skysmith/magic-character-box/tests/test_wifi.py

from __future__ import annotations

import json
import subprocess
import unittest

from magic_box.wifi import WifiController


class WifiControllerTests(unittest.TestCase):
    def test_status_uses_privileged_helper_when_available(self) -> None:
        runner = _FakeRunner(
            {
                ("/usr/local/bin/magic-character-box-wifi-control", "radio-status"): subprocess.CompletedProcess(
                    [], 0, "enabled\n", ""
                ),
                ("/usr/local/bin/magic-character-box-wifi-control", "device-status"): subprocess.CompletedProcess(
                    [], 0, "wlan0:wifi:connected:Mini Cottage\n", ""
                ),
            }
        )
        controller = WifiController(
            nmcli=None,
            helper="/usr/local/bin/magic-character-box-wifi-control",
            sudo="",
            runner=runner,
        )

        status = controller.status()

        self.assertTrue(status.available)
        self.assertTrue(status.connected)
        self.assertEqual(status.ssid, "Mini Cottage")
        self.assertEqual(
            runner.commands,
            [
                ("/usr/local/bin/magic-character-box-wifi-control", "radio-status"),
                ("/usr/local/bin/magic-character-box-wifi-control", "device-status"),
            ],
        )

    def test_connect_uses_helper_without_leaking_password_in_result(self) -> None:
        runner = _FakeRunner(
            {
                ("/usr/local/bin/magic-character-box-wifi-control", "connect-stdin"): subprocess.CompletedProcess(
                    [], 0, "connected\n", ""
                ),
                ("/usr/local/bin/magic-character-box-wifi-control", "radio-status"): subprocess.CompletedProcess(
                    [], 0, "enabled\n", ""
                ),
                ("/usr/local/bin/magic-character-box-wifi-control", "device-status"): subprocess.CompletedProcess(
                    [], 0, "wlan0:wifi:connected:Mini Cottage\n", ""
                ),
            }
        )
        controller = WifiController(
            nmcli=None,
            helper="/usr/local/bin/magic-character-box-wifi-control",
            sudo="",
            runner=runner,
        )

        result = controller.connect("Mini Cottage", "private pass")

        self.assertTrue(result.ok)
        self.assertEqual(result.message, "Connected to Mini Cottage.")
        self.assertNotIn("private pass", result.to_dict()["message"])
        self.assertEqual(
            runner.commands[0],
            ("/usr/local/bin/magic-character-box-wifi-control", "connect-stdin"),
        )
        self.assertNotIn("private pass", " ".join(runner.commands[0]))
        self.assertEqual(
            json.loads(runner.inputs[0] or ""),
            {"ssid": "Mini Cottage", "password": "private pass"},
        )

    def test_connect_recovers_from_r24_helper_missing_json_import(self) -> None:
        runner = _FakeRunner(
            {
                ("/usr/local/bin/magic-character-box-wifi-control", "connect-stdin"): subprocess.CompletedProcess(
                    [], 1, "", "NameError: name 'json' is not defined\n"
                ),
                ("/usr/bin/nmcli", "--ask", "device", "wifi", "connect", "Mini Cottage"):
                    subprocess.CompletedProcess([], 0, "connected\n", ""),
                ("/usr/local/bin/magic-character-box-wifi-control", "radio-status"): subprocess.CompletedProcess(
                    [], 0, "enabled\n", ""
                ),
                ("/usr/local/bin/magic-character-box-wifi-control", "device-status"): subprocess.CompletedProcess(
                    [], 0, "wlan0:wifi:connected:Mini Cottage\n", ""
                ),
            }
        )
        controller = WifiController(
            nmcli="/usr/bin/nmcli",
            helper="/usr/local/bin/magic-character-box-wifi-control",
            sudo="",
            runner=runner,
        )

        result = controller.connect("Mini Cottage", "private pass")

        self.assertTrue(result.ok)
        self.assertEqual(
            runner.commands[:2],
            [
                ("/usr/local/bin/magic-character-box-wifi-control", "connect-stdin"),
                ("/usr/bin/nmcli", "--ask", "device", "wifi", "connect", "Mini Cottage"),
            ],
        )
        self.assertNotIn("private pass", " ".join(runner.commands[1]))
        self.assertEqual(runner.inputs[1], "private pass\n")

    def test_change_recovery_password_uses_helper_without_leaking_password(self) -> None:
        runner = _FakeRunner(
            {
                (
                    "/usr/local/bin/magic-character-box-wifi-control",
                    "set-recovery-password-stdin",
                ): subprocess.CompletedProcess([], 0, "", ""),
                ("/usr/local/bin/magic-character-box-wifi-control", "radio-status"): subprocess.CompletedProcess(
                    [], 0, "enabled\n", ""
                ),
                ("/usr/local/bin/magic-character-box-wifi-control", "device-status"): subprocess.CompletedProcess(
                    [], 0, "wlan0:wifi:connected:story-dock-setup-hotspot\n", ""
                ),
            }
        )
        controller = WifiController(
            nmcli=None,
            helper="/usr/local/bin/magic-character-box-wifi-control",
            sudo="",
            runner=runner,
        )

        result = controller.change_recovery_password("new private pass")

        self.assertTrue(result.ok)
        self.assertNotIn("new private pass", result.message)
        self.assertEqual(
            runner.commands[0],
            (
                "/usr/local/bin/magic-character-box-wifi-control",
                "set-recovery-password-stdin",
            ),
        )
        self.assertNotIn("new private pass", " ".join(runner.commands[0]))
        self.assertEqual(json.loads(runner.inputs[0] or ""), {"password": "new private pass"})

    def test_change_recovery_password_rejects_invalid_length(self) -> None:
        controller = WifiController(nmcli="/usr/bin/nmcli", helper=None, sudo="")

        with self.assertRaisesRegex(ValueError, "8–63"):
            controller.change_recovery_password("short")


class _FakeRunner:
    def __init__(self, results: dict[tuple[str, ...], subprocess.CompletedProcess[str]]) -> None:
        self.results = results
        self.commands: list[tuple[str, ...]] = []
        self.inputs: list[str | None] = []

    def __call__(self, command: list[str], **kwargs: object) -> subprocess.CompletedProcess[str]:
        key = tuple(command)
        self.commands.append(key)
        value = kwargs.get("input")
        self.inputs.append(value if isinstance(value, str) else None)
        return self.results.get(key, subprocess.CompletedProcess(command, 1, "", f"unexpected command: {key}"))


if __name__ == "__main__":
    unittest.main()
